svenpetersen1965/C64-Keyboard-Controlled-Kernal-Switch/Rev. 0/inkscape/EXROM_Timing.png

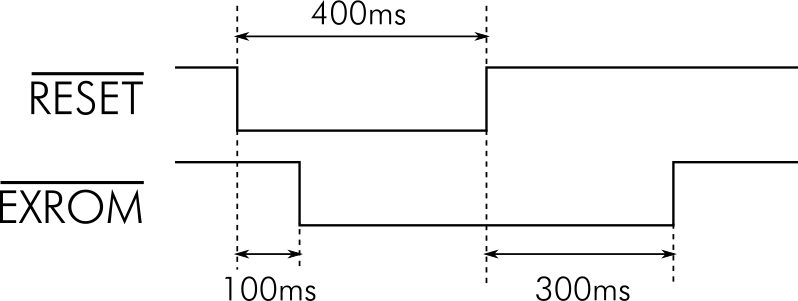
Rev. 0/inkscape/EXROM_Timing.png
