svenpetersen1965/C64-Keyboard-Controlled-Kernal-Switch/Rev. 1/inkscape/C64_Keyb_KSw_ISP_J2.png

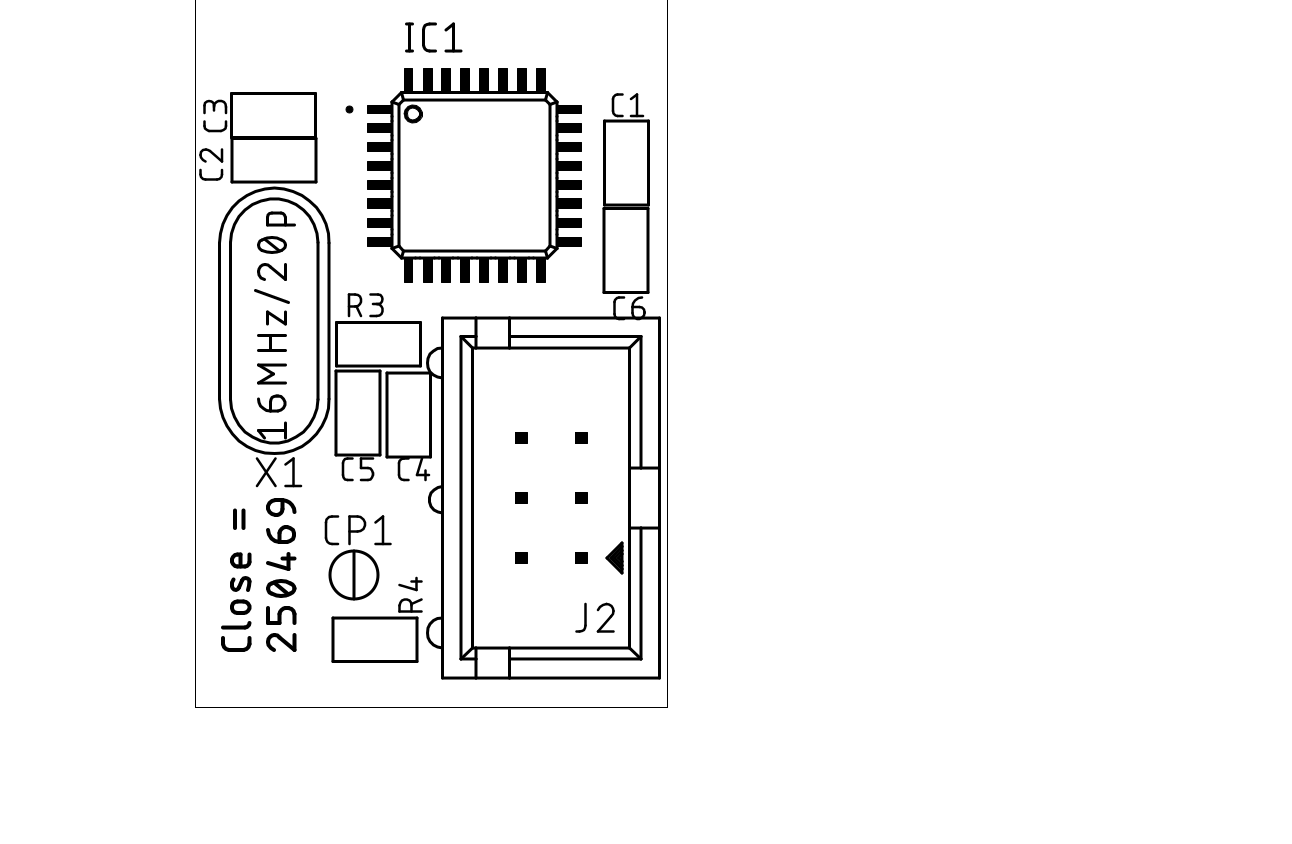
Rev. 1/inkscape/C64_Keyb_KSw_ISP_J2.png
