svenpetersen1965/C64-Keyboard-Controlled-Kernal-Switch/Rev. 1/pictures/3481_-_EXROM_Pin.JPG

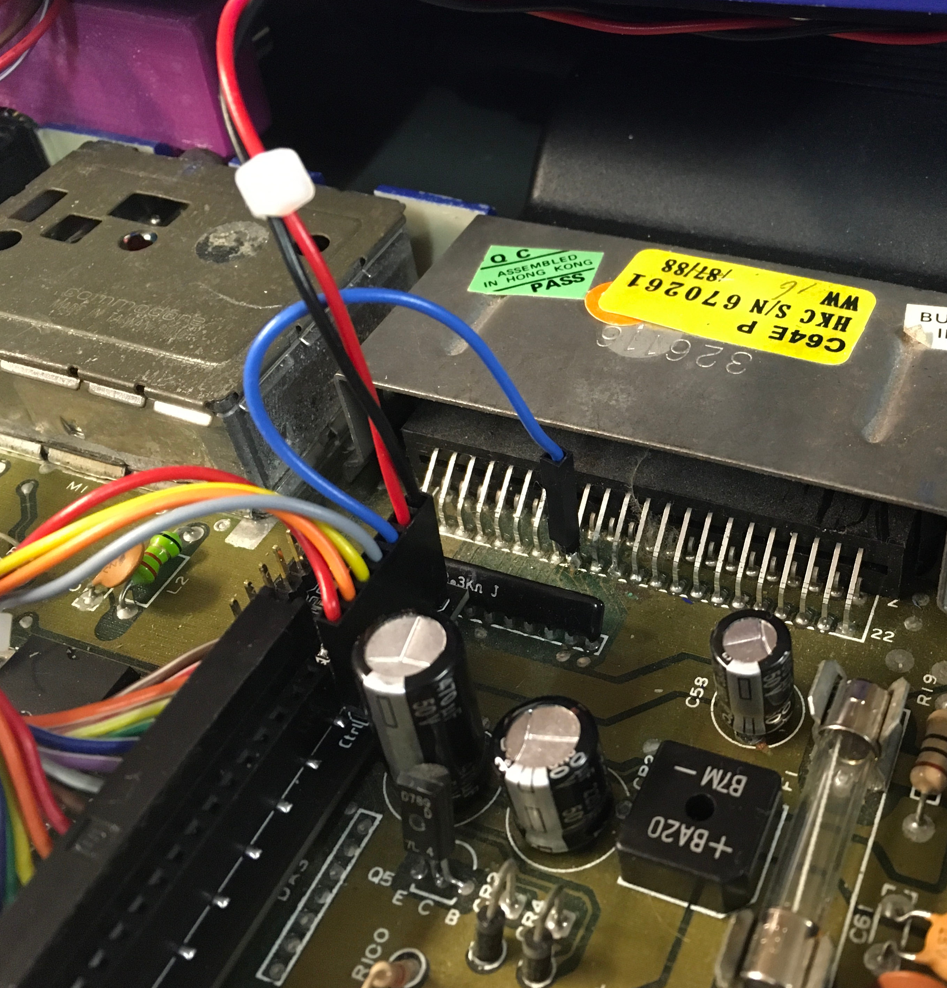
Rev. 1/pictures/3481_-_EXROM_Pin.JPG
