svenpetersen1965/C64-Keyboard-Controlled-Kernal-Switch/Rev. 1/pictures/3482_-_EXROM_location.JPG

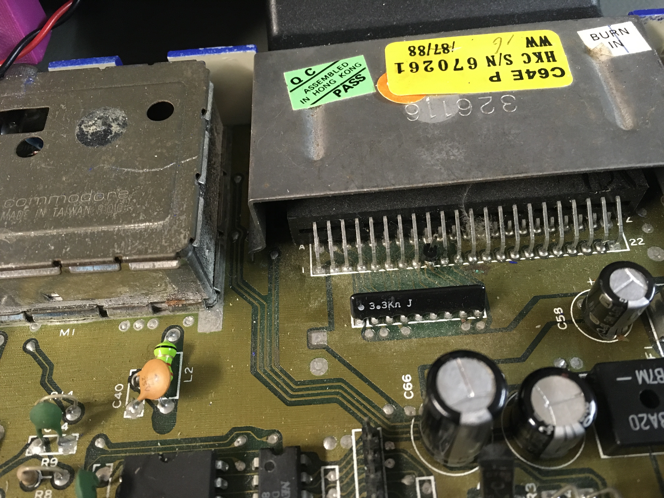
Rev. 1/pictures/3482_-_EXROM_location.JPG
