svenpetersen1965/C64-Keyboard-Controlled-Kernal-Switch/Rev. 1/pictures/C64_Keyb_KSw_J3_J4.png

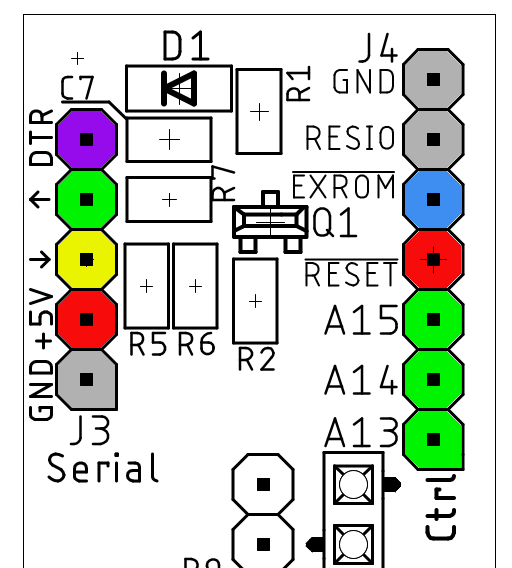
Rev. 1/pictures/C64_Keyb_KSw_J3_J4.png
