svenpetersen1965/C64-Keyboard-Controlled-Kernal-Switch/Rev. 1/pictures/CP1_Short_Board.JPG

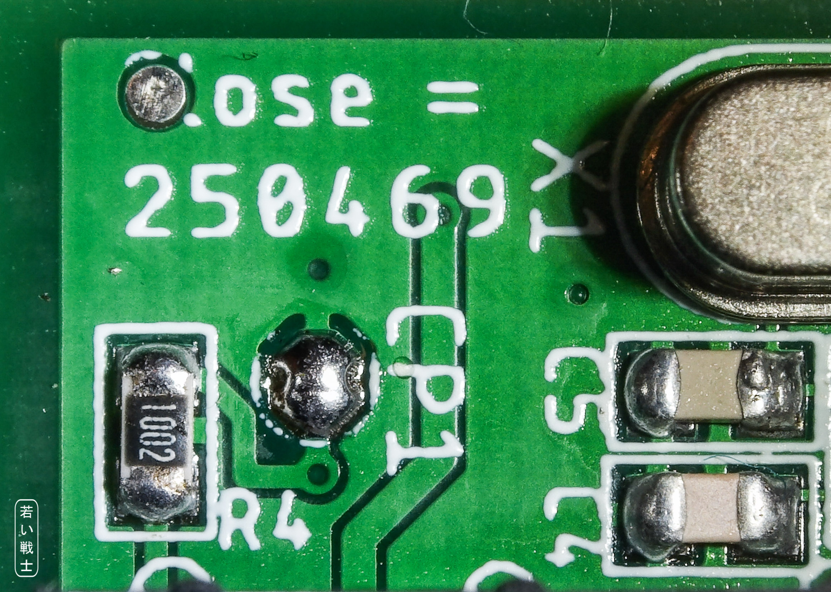
Rev. 1/pictures/CP1_Short_Board.JPG
