svenpetersen1965/C64-Keyboard-Controlled-Kernal-Switch/Rev. 1/pictures/IMG_3534.JPG

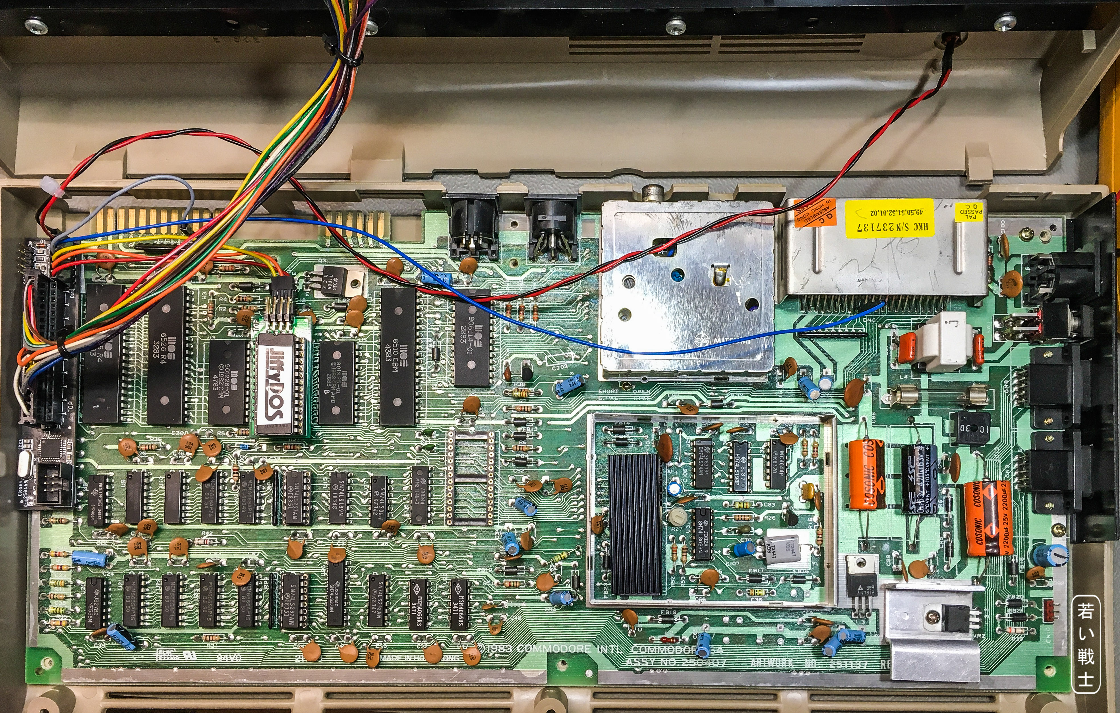
Rev. 1/pictures/IMG_3534.JPG
